TUDSSL/condenar/Hardware/PCBs/CPUModule/panel/readme.md

 kikit panelize     --layout 'grid; rows: 1; cols: 1; space: 2mm'     --tabs 'fixed; width: 3mm; vcount: 2'     --cuts 'mousebites; drill: 0.5mm; spacing: 1mm; offset: -0.15mm; prolong: 0.5mm'     --framing 'frame; width: 5mm; space: 3mm; cuts: h'     --post 'millradius: 1mm'     ../cpu-module.kicad_pcb cpu-module-panel.kicad_pcb
