TUDSSL/condenar/Data/ConsoleBenchmarks/SSD1963_PowerConsumption.xlsx

 |  |  |  | Power consumption [mA]
 |  |  |  |  |  | CLK settings
 |  |  |  |  |  | APO 48MHz | APO 24MHz | APO 12MHz | APO 6MHz | XTAL -> 6MHz | XTAL -> PLL 100MHz | XTAL -> PLL 50MHz | APO -> PLL 100MHz | APO -> PLL 50MHz
40Hz | 4.4 | APO_48MHz, 10Hz | 1.8mA | FPS | 10Hz | 1.8 | 1.05 | 0.67 | 0.47 | 0.725 | 4.2 | 2.7 | 3.95 | 2.45
20Hz | 2.7 | APO_48MHz, 20Hz | 1.92mA |  | 20Hz | 1.92 | 1.08 | 0.77 | 0.58 | 0.839 | 4.3 | 2.8 | 4.09 | 2.53
10Hz | 1.86 | APO_48MHz, 40Hz | 2.14mA |  | 40Hz | 2.14 | 1.37 | 0.98 |  |  | 4.4 | 3 | 4.3 | 2.75
 |  | APO_24MHz, 10Hz | 1.05mA
 |  | APO_24MHz, 20Hz | 1.08mA
 |  | APO_24MHz, 40Hz | 1.37mA
