TUDSSL/condenar/Data/MainStudy/Data/SurveyResults/Complete_Survey_Data.csv

participant_id | experiment_option | lux_level | freq_gaming_background | fps_background | puzzle_background | doom_background | tetris_background | power_harvesting_background | device_type | performance_effort | temporal_frustration | effort_temporal | physical_frustration | performance_frustration | physical_temporal | performance_physical | mental_temporal | effort_frustration | mental_performance | performance_temporal | mental_effort | mental_physical | effort_physical | mental_frustration | tetris_a_experience_vs_doing | tetris_a_emotional_attachment | tetris_a_interest_in_progress | tetris_a_desire_to_speak | tetris_a_disappointment_when_interrupted | tetris_a_desire_to_play_again | tetris_a_mental_demand | tetris_a_physical_demand | tetris_a_hurried_pace | tetris_a_success_accomplishment | tetris_a_effort | tetris_a_insecurity_irritation | doom_a_experience_vs_doing | doom_a_emotional_attachment | doom_a_interest_in_progress | doom_a_desire_to_speak | doom_a_disappointment_when_interrupted | doom_a_desire_to_play_again | doom_a_mental_demand | doom_a_physical_demand | doom_a_hurried_pace | doom_a_success_accomplishment | doom_a_effort | doom_a_insecurity_irritation |
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
