TUDSSL/condenar/Software/Console/games/Gameboy/GBA/emulator/gba/MMU.cpp

#include "../common/Port.h"
#include "../common/Settings.h"
#include "Cartridge.h"
#include "CPU.h"
#include "GBA.h"
#include "Globals.h"
#include <cstdio>
#include "string.h"
#include "Helpers/Flash.h"


extern "C"{
	uint32_t am_util_stdio_printf(const char *pcFmt, ...);
}



extern bool stopState;
extern bool timer0On;
extern int timer0Ticks;
extern int timer0ClockReload;
extern bool timer1On;
extern int timer1Ticks;
extern int timer1ClockReload;
extern bool timer2On;
extern int timer2Ticks;
extern int timer2ClockReload;
extern bool timer3On;
extern int timer3Ticks;
extern int timer3ClockReload;

namespace MMU
{

static bool ioReadable[0x400];

template <typename T>
static inline T readLE(u8* x)
{
	return *((T *)x);
}

template <typename T>
static inline void writeLE(u8* x, T value)
{
	*((T *)x) = value;
}

// Memory read functions forward declarations
template<typename T>
static T unreadable(u32 address);

template<int s, typename T>
static T readGeneric(u32 address);

template<typename T, int mask>
static T readBios(u32 address);
 
template<typename T>
static T readVRAM(u32 address);

static u8 readIo8(u32 address);
static u16 readIo16(u32 address);
static u32 readIo32(u32 address);

// Memory write functions forward declarations
template<typename T>
static void unwritable(u32 address, T value);
 
template<int s, typename T>
static void writeGeneric(u32 address, T value);

template<int s>
static void writeVideo8(u32 address, u8 value);

template<typename T>
static void writeVRAM(u32 address, T value);

template<>
void writeVRAM<u8>(u32 address, u8 value);

static void writeIo8(u32 address, u8 value);
static void writeIo16(u32 address, u16 value);
static void writeIo32(u32 address, u32 value);

// Memory map definition
struct MemAccess
{
	u8 *mem;
	const u32 mask;
	u8 (*read8)(u32);
	u16 (*read16)(u32);
	u32 (*read32)(u32);
	void (*write8)(u32, u8);
	void (*write16)(u32, u16);
	void (*write32)(u32, u32);
};

static MemAccess memMap[] =
{
	{ 0, 0x00003FFF, readBios<u8, 0x03>, readBios<u16, 0x02>, readBios<u32, 0x0F>, unwritable<u8>,      unwritable<u16>,      unwritable<u32>      }, // 0 - bios - mask values are probably wrong
	{ 0, 0x00000000, unreadable<u8>,     unreadable<u16>,     unreadable<u32>,     unwritable<u8>,      unwritable<u16>,      unwritable<u32>      }, // 1
	{ 0, 0x0003FFFF, readGeneric<2, u8>, readGeneric<2, u16>, readGeneric<2, u32>, writeGeneric<2, u8>, writeGeneric<2, u16>, writeGeneric<2, u32> }, // 2
	{ 0, 0x00007FFF, readGeneric<3, u8>, readGeneric<3, u16>, readGeneric<3, u32>, writeGeneric<3, u8>, writeGeneric<3, u16>, writeGeneric<3, u32> }, // 3
	{ 0, 0x000003FF, readIo8,            readIo16,            readIo32,            writeIo8,            writeIo16,            writeIo32            }, // 4
	{ 0, 0x000003FF, readGeneric<5, u8>, readGeneric<5, u16>, readGeneric<5, u32>, writeVideo8<5>,      writeGeneric<5, u16>, writeGeneric<5, u32> }, // 5
	{ 0, 0x0001FFFF, readVRAM<u8>,       readVRAM<u16>,       readVRAM<u32>,       writeVRAM<u8>,       writeVRAM<u16>,       writeVRAM<u32>       }, // 6
	{ 0, 0x000003FF, readGeneric<7, u8>, readGeneric<7, u16>, readGeneric<7, u32>, unwritable<u8>,      writeGeneric<7, u16>, writeGeneric<7, u32> }, // 7
	{ 0, 0xFFFFFFFF, cartridge_read8,   cartridge_read16,   cartridge_read32,   cartridge_write8,   cartridge_write16,   cartridge_write32   }, // 8
	{ 0, 0xFFFFFFFF, cartridge_read8,   cartridge_read16,   cartridge_read32,   cartridge_write8,   cartridge_write16,   cartridge_write32   }, // 9
	{ 0, 0xFFFFFFFF, cartridge_read8,   cartridge_read16,   cartridge_read32,   cartridge_write8,   cartridge_write16,   cartridge_write32   }, // 10
	{ 0, 0xFFFFFFFF, cartridge_read8,   cartridge_read16,   cartridge_read32,   cartridge_write8,   cartridge_write16,   cartridge_write32   }, // 11
	{ 0, 0xFFFFFFFF, cartridge_read8,   cartridge_read16,   cartridge_read32,   cartridge_write8,   cartridge_write16,   cartridge_write32   }, // 12
	{ 0, 0xFFFFFFFF, cartridge_read8,   cartridge_read16,   cartridge_read32,   cartridge_write8,   cartridge_write16,   cartridge_write32   }, // 13
	{ 0, 0xFFFFFFFF, cartridge_read8,   cartridge_read16,   cartridge_read32,   cartridge_write8,   cartridge_write16,   cartridge_write32   }  // 14
};

// MMU public functions
bool init()
{	
	//Fast clear of the memory, just in case
	memset((uint8_t*)SRAM_XIP_BASE_ADDRESS, 0, 0x40000 + 0x4000 + 0x8000 + 0x400 + 0x20000 + 0x400 + 0x400);


	workRAM     = (uint8_t*)SRAM_XIP_BASE_ADDRESS; //   new u8[0x40000];
	bios        = workRAM + 0x40000; //new u8[0x4000];
	internalRAM = bios + 0x4000; //new u8[0x8000];
	paletteRAM  = internalRAM + 0x8000; //new u8[0x400];
	vram        = paletteRAM + 0x400; //new u8[0x20000];
	oam         = vram + 0x20000; //new u8[0x400];
	ioMem       = oam + 0x400; //new u8[0x400];
	//End of shared memory used: (ioMem + 0x400). Total memory: 445,440B







	memMap[0].mem = bios;
	memMap[2].mem = workRAM;
	memMap[3].mem = internalRAM;
	memMap[4].mem = ioMem;
	memMap[5].mem = paletteRAM;
	memMap[6].mem = vram;
	memMap[7].mem = oam;
	
	for (int i = 0; i < 0x400; i++)
		ioReadable[i] = true;
	for (int i = 0x10; i < 0x48; i++)
		ioReadable[i] = false;
	for (int i = 0x4c; i < 0x50; i++)
		ioReadable[i] = false;
	for (int i = 0x54; i < 0x60; i++)
		ioReadable[i] = false;
	for (int i = 0x8c; i < 0x90; i++)
		ioReadable[i] = false;
	for (int i = 0xa0; i < 0xb8; i++)
		ioReadable[i] = false;
	for (int i = 0xbc; i < 0xc4; i++)
		ioReadable[i] = false;
	for (int i = 0xc8; i < 0xd0; i++)
		ioReadable[i] = false;
	for (int i = 0xd4; i < 0xdc; i++)
		ioReadable[i] = false;
	for (int i = 0xe0; i < 0x100; i++)
		ioReadable[i] = false;
	for (int i = 0x110; i < 0x120; i++)
		ioReadable[i] = false;
	for (int i = 0x12c; i < 0x130; i++)
		ioReadable[i] = false;
	for (int i = 0x138; i < 0x140; i++)
		ioReadable[i] = false;
	for (int i = 0x144; i < 0x150; i++)
		ioReadable[i] = false;
	for (int i = 0x15c; i < 0x200; i++)
		ioReadable[i] = false;
	for (int i = 0x20c; i < 0x300; i++)
		ioReadable[i] = false;
	for (int i = 0x304; i < 0x400; i++)
		ioReadable[i] = false;

	return true;
}


u32 read32(u32 address)
{
 #ifdef GBA_LOGGING
	if (address & 3)
	{
		if (settings_log_channel_enabled(LOG_UNALIGNED_MEMORY))
 		{
			am_util_stdio_printf("Unaligned word read: %08x at %08x\n", address, CPU::armMode ?
 			    CPU::armNextPC - 4 : CPU::armNextPC - 2);
 		}
	}
 #endif
 
	// Reads must be 32 bits aligned
	u32 value =  memMap[address >> 24].read32(address & 0xFFFFFFFC);
 
 	if (address & 3)
 	{
 		int shift = (address & 3) << 3;
 		value = (value >> shift) | (value << (32 - shift));
 	}

 	return value;
 }
 
u32 read16(u32 address)
 {
 #ifdef GBA_LOGGING
 	if (address & 1)
	{
		if (settings_log_channel_enabled(LOG_UNALIGNED_MEMORY))
		{
			am_util_stdio_printf("Unaligned word read: %08x at %08x\n", address, CPU::armMode ?
			    CPU::armNextPC - 4 : CPU::armNextPC - 2);
		}
	}
#endif

	// Reads must be 16 bits aligned
	u16 value = memMap[address >> 24].read16(address & 0xFFFFFFFE);

	if (address & 1)
	{
		value = (value >> 8) | (value << 24);
	}

	return value;
}

u16 read16s(u32 address)
{
	u16 value = read16(address);
	if ((address & 1))
		value = (s8)value;
	return value;
}

u8 read8(u32 address)
{
	return memMap[address >> 24].read8(address);
}

void write32(u32 address, u32 value)
{
#ifdef GBA_LOGGING
	if (address & 3)
	{
		if (settings_log_channel_enabled(LOG_UNALIGNED_MEMORY))
		{
			am_util_stdio_printf("Unaligned word write: %08x to %08x from %08x\n",
			    value,
			    address,
			    CPU::armMode ? CPU::armNextPC - 4 : CPU::armNextPC - 2);
		}
	}
#endif

	memMap[address >> 24].write32(address & 0xFFFFFFFC, value);
}

void write16(u32 address, u16 value)
{
#ifdef GBA_LOGGING
	if (address & 1)
	{
		if (settings_log_channel_enabled(LOG_UNALIGNED_MEMORY))
		{
			am_util_stdio_printf("Unaligned halfword write: %04x to %08x from %08x\n",
			    value,
			    address,
			    CPU::armMode ? CPU::armNextPC - 4 : CPU::armNextPC - 2);
		}
	}
#endif

	memMap[address >> 24].write16(address & 0xFFFFFFFE, value);
}

void write8(u32 address, u8 b)
{
	memMap[address >> 24].write8(address, b);
}

// Memory read functions implementations
template<typename T>
static T unreadable(u32 address)
{
#ifdef GBA_LOGGING
		if (settings_log_channel_enabled(LOG_ILLEGAL_READ))
		{
			am_util_stdio_printf("Illegal read: %08x at %08x\n", address, CPU::armMode ?
			    CPU::armNextPC - 4 : CPU::armNextPC - 2);
		}
#endif

	return 0;
}

template<int s, typename T>
static T readGeneric(u32 address)
{
	u32 mask = memMap[s].mask;

	return readLE<T>(&memMap[s].mem[address & mask]);
}

template<typename T, int mask>
static T readBios(u32 address)
{
	T value;

	if (CPU::reg[15].I >> 24)
	{
		// TODO: proper handling of reading unreadable bios memory, without "biosProtected"
		if (address < 0x4000)
		{
			value = readLE<T>(&biosProtected[address & mask]);
			//LOG_I("Reading protected bios memory %d %d\n", address, value);
		}
		else
		{
			value = unreadable<T>(address);
		}
	}
	else
		value = readGeneric<0, T>(address);

	return value;
}

static u8 readIo8(u32 address)
{
	if ((address < 0x4000400) && ioReadable[address & 0x3FF])
	{
		return readGeneric<4, u8>(address);
	}
	else
	{
		return unreadable<u8>(address);
	}
}

static u16 readIo16(u32 address)
{
	u16 value;

	if ((address < 0x4000400) && ioReadable[address & 0x3FF])
	{
		value = readGeneric<4, u16>(address);
		if (((address & 0x3fe)>0xFF) && ((address & 0x3fe)<0x10E))
		{
			if (((address & 0x3fe) == 0x100) && timer0On)
				value = 0xFFFF - ((timer0Ticks-cpuTotalTicks) >> timer0ClockReload);
			else
				if (((address & 0x3fe) == 0x104) && timer1On && !(TM1CNT & 4))
					value = 0xFFFF - ((timer1Ticks-cpuTotalTicks) >> timer1ClockReload);
				else
					if (((address & 0x3fe) == 0x108) && timer2On && !(TM2CNT & 4))
						value = 0xFFFF - ((timer2Ticks-cpuTotalTicks) >> timer2ClockReload);
					else
						if (((address & 0x3fe) == 0x10C) && timer3On && !(TM3CNT & 4))
							value = 0xFFFF - ((timer3Ticks-cpuTotalTicks) >> timer3ClockReload);
		}
	}
	else
	{
		value = unreadable<u16>(address);
	}

	return value;
}

static u32 readIo32(u32 address)
{
	u32 value;

	if ((address < 0x4000400) && ioReadable[address & 0x3FF])
	{
		if (ioReadable[(address & 0x3FF) + 2])
			value = readGeneric<4, u32>(address);
		else
			value = readGeneric<4, u16>(address);
	}
	else
	{
		value = unreadable<u32>(address);
	}

	return value;
}

template<typename T>
static T readVRAM(u32 address)
{
	address &= 0x1FFFF;

	if (((DISPCNT & 7) > 2) && ((address & 0x1C000) == 0x18000))
	{
		return 0;
	}
	if ((address & 0x18000) == 0x18000)
	{
		address &= 0x17FFF;
	}

	return readGeneric<6, T>(address);
}

// Memory write functions implementations
template<typename T>
static void unwritable(u32 address, T value)
{
#ifdef GBA_LOGGING
	if (settings_log_channel_enabled(LOG_ILLEGAL_WRITE))
	{
		am_util_stdio_printf("Illegal write: %02x to %08x from %08x\n",
			value,
			address,
			CPU::armMode ? CPU::armNextPC - 4 : CPU::armNextPC - 2);
	}
#endif
}

template<int s, typename T>
static void writeGeneric(u32 address, T value)
{
	u32 mask = memMap[s].mask;

	writeLE<T>(&memMap[s].mem[address & mask], value);
}

template<int s>
static void writeVideo8(u32 address, u8 value)
{
	writeGeneric<s, u16>(address & 0xFFFFFFFE, (value << 8) | value);
}

template<typename T>
static void writeVRAM(u32 address, T value)
{
	address = (address & 0x1FFFF);
	if (((DISPCNT & 7) > 2) && ((address & 0x1C000) == 0x18000))
		return;
	if ((address & 0x18000) == 0x18000)
		address &= 0x17FFF;

	writeGeneric<6, T>(address, value);
}

template<>
void writeVRAM<u8>(u32 address, u8 value)
{
	static const u32 objTilesAddress [3] = {0x010000, 0x014000, 0x014000};

	address &= 0x1FFFF;
	if (((DISPCNT & 7) > 2) && ((address & 0x1C000) == 0x18000))
		return;
	if ((address & 0x18000) == 0x18000)
		address &= 0x17FFF;

	// byte writes to OBJ VRAM are ignored
	if (address < objTilesAddress[((DISPCNT&7)+1)>>2])
	{
		writeVideo8<6>(address, value);
	}
}

static void writeIo8(u32 address, u8 value)
{
	if (address < 0x4000400)
	{
		switch (address & 0x3FF)
		{
		case 0x60:
		case 0x61:
		case 0x62:
		case 0x63:
		case 0x64:
		case 0x65:
		case 0x68:
		case 0x69:
		case 0x6c:
		case 0x6d:
		case 0x70:
		case 0x71:
		case 0x72:
		case 0x73:
		case 0x74:
		case 0x75:
		case 0x78:
		case 0x79:
		case 0x7c:
		case 0x7d:
		case 0x80:
		case 0x81:
		case 0x84:
		case 0x85:
		case 0x90:
		case 0x91:
		case 0x92:
		case 0x93:
		case 0x94:
		case 0x95:
		case 0x96:
		case 0x97:
		case 0x98:
		case 0x99:
		case 0x9a:
		case 0x9b:
		case 0x9c:
		case 0x9d:
		case 0x9e:
		case 0x9f:
			//soundEvent(address & 0xFF, value);
			break;
		case 0x301: // HALTCNT, undocumented
			if (value == 0x80)
				stopState = true;
			holdState = 1;
			cpuNextEvent = cpuTotalTicks;
			break;
		default: // every other register
			u32 lowerBits = address & 0x3fe;
			if (address & 1)
			{
				CPUUpdateRegister(lowerBits, (READ16LE(&ioMem[lowerBits]) & 0x00FF) | (value << 8));
			}
			else
			{
				CPUUpdateRegister(lowerBits, (READ16LE(&ioMem[lowerBits]) & 0xFF00) | value);
			}
		}
	}
	else
	{
		unwritable<u8>(address, value);
	}
}

static void writeIo16(u32 address, u16 value)
{
	if (address < 0x4000400)
	{
		CPUUpdateRegister(address & 0x3FF, value);
	}
	else
	{
		unwritable<u16>(address, value);
	}
}

static void writeIo32(u32 address, u32 value)
{
	if (address < 0x4000400)
	{
		CPUUpdateRegister((address & 0x3FF), value & 0xFFFF);
		CPUUpdateRegister((address & 0x3FF) + 2, (value >> 16));
	}
	else
	{
		unwritable<u32>(address, value);
	}
}

} // namespace MMU
