TUDSSL/condenar/Software/Console/games/Gameboy/GBA/emulator/gba/Globals.c

// VisualBoyAdvance - Nintendo Gameboy/GameboyAdvance (TM) emulator.
// Copyright (C) 1999-2003 Forgotten
// Copyright (C) 2005-2006 Forgotten and the VBA development team

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
#include "Globals.h"

int layerEnable = 0xff00;

u8 *bios = 0;
u8 *internalRAM = 0;
u8 *workRAM = 0;
u8 *paletteRAM = 0;
u8 *vram = 0;
u8 *oam = 0;
u8 *ioMem = 0;

/*
	workRAM     = new u8[0x40000];
	bios        = new u8[0x4000];
	internalRAM = new u8[0x8000];
	paletteRAM  = new u8[0x400];
	vram        = new u8[0x20000];
	oam         = new u8[0x400];
	ioMem       = new u8[0x400];
*/

u16 DISPCNT  = 0x0080;
u16 DISPSTAT = 0x0000;
u16 VCOUNT   = 0x0000;
u16 BG0CNT   = 0x0000;
u16 BG1CNT   = 0x0000;
u16 BG2CNT   = 0x0000;
u16 BG3CNT   = 0x0000;
u16 BG0HOFS  = 0x0000;
u16 BG0VOFS  = 0x0000;
u16 BG1HOFS  = 0x0000;
u16 BG1VOFS  = 0x0000;
u16 BG2HOFS  = 0x0000;
u16 BG2VOFS  = 0x0000;
u16 BG3HOFS  = 0x0000;
u16 BG3VOFS  = 0x0000;
u16 BG2PA    = 0x0100;
u16 BG2PB    = 0x0000;
u16 BG2PC    = 0x0000;
u16 BG2PD    = 0x0100;
u16 BG2X_L   = 0x0000;
u16 BG2X_H   = 0x0000;
u16 BG2Y_L   = 0x0000;
u16 BG2Y_H   = 0x0000;
u16 BG3PA    = 0x0100;
u16 BG3PB    = 0x0000;
u16 BG3PC    = 0x0000;
u16 BG3PD    = 0x0100;
u16 BG3X_L   = 0x0000;
u16 BG3X_H   = 0x0000;
u16 BG3Y_L   = 0x0000;
u16 BG3Y_H   = 0x0000;
u16 WIN0H    = 0x0000;
u16 WIN1H    = 0x0000;
u16 WIN0V    = 0x0000;
u16 WIN1V    = 0x0000;
u16 WININ    = 0x0000;
u16 WINOUT   = 0x0000;
u16 MOSAIC   = 0x0000;
u16 BLDMOD   = 0x0000;
u16 COLEV    = 0x0000;
u16 COLY     = 0x0000;
u16 DM0SAD_L = 0x0000;
u16 DM0SAD_H = 0x0000;
u16 DM0DAD_L = 0x0000;
u16 DM0DAD_H = 0x0000;
u16 DM0CNT_L = 0x0000;
u16 DM0CNT_H = 0x0000;
u16 DM1SAD_L = 0x0000;
u16 DM1SAD_H = 0x0000;
u16 DM1DAD_L = 0x0000;
u16 DM1DAD_H = 0x0000;
u16 DM1CNT_L = 0x0000;
u16 DM1CNT_H = 0x0000;
u16 DM2SAD_L = 0x0000;
u16 DM2SAD_H = 0x0000;
u16 DM2DAD_L = 0x0000;
u16 DM2DAD_H = 0x0000;
u16 DM2CNT_L = 0x0000;
u16 DM2CNT_H = 0x0000;
u16 DM3SAD_L = 0x0000;
u16 DM3SAD_H = 0x0000;
u16 DM3DAD_L = 0x0000;
u16 DM3DAD_H = 0x0000;
u16 DM3CNT_L = 0x0000;
u16 DM3CNT_H = 0x0000;
u16 TM0D     = 0x0000;
u16 TM0CNT   = 0x0000;
u16 TM1D     = 0x0000;
u16 TM1CNT   = 0x0000;
u16 TM2D     = 0x0000;
u16 TM2CNT   = 0x0000;
u16 TM3D     = 0x0000;
u16 TM3CNT   = 0x0000;
u16 P1       = 0xFFFF;
u16 IE       = 0x0000;
u16 IF       = 0x0000;
u16 IME      = 0x0000;
