TUDSSL/condenar/Software/Console/games/Gameboy/GBA/emulator/gba/Globals.h

// VisualBoyAdvance - Nintendo Gameboy/GameboyAdvance (TM) emulator.
// Copyright (C) 1999-2003 Forgotten
// Copyright (C) 2005-2006 Forgotten and the VBA development team

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
#ifndef VBAM_GBA_GLOBALS_H_
#define VBAM_GBA_GLOBALS_H_

#include <glib.h>
#include "../common/Types.h"

/* Set up for C function definitions, even when using C++ */
#ifdef __cplusplus
extern "C" {
#endif

extern int layerEnable;

extern u8 *bios;
extern u8 *internalRAM;
extern u8 *workRAM;
extern u8 *paletteRAM;
extern u8 *vram;
extern u8 *oam;
extern u8 *ioMem;

extern u16 DISPCNT;
extern u16 DISPSTAT;
extern u16 VCOUNT;
extern u16 BG0CNT;
extern u16 BG1CNT;
extern u16 BG2CNT;
extern u16 BG3CNT;
extern u16 BG0HOFS;
extern u16 BG0VOFS;
extern u16 BG1HOFS;
extern u16 BG1VOFS;
extern u16 BG2HOFS;
extern u16 BG2VOFS;
extern u16 BG3HOFS;
extern u16 BG3VOFS;
extern u16 BG2PA;
extern u16 BG2PB;
extern u16 BG2PC;
extern u16 BG2PD;
extern u16 BG2X_L;
extern u16 BG2X_H;
extern u16 BG2Y_L;
extern u16 BG2Y_H;
extern u16 BG3PA;
extern u16 BG3PB;
extern u16 BG3PC;
extern u16 BG3PD;
extern u16 BG3X_L;
extern u16 BG3X_H;
extern u16 BG3Y_L;
extern u16 BG3Y_H;
extern u16 WIN0H;
extern u16 WIN1H;
extern u16 WIN0V;
extern u16 WIN1V;
extern u16 WININ;
extern u16 WINOUT;
extern u16 MOSAIC;
extern u16 BLDMOD;
extern u16 COLEV;
extern u16 COLY;
extern u16 DM0SAD_L;
extern u16 DM0SAD_H;
extern u16 DM0DAD_L;
extern u16 DM0DAD_H;
extern u16 DM0CNT_L;
extern u16 DM0CNT_H;
extern u16 DM1SAD_L;
extern u16 DM1SAD_H;
extern u16 DM1DAD_L;
extern u16 DM1DAD_H;
extern u16 DM1CNT_L;
extern u16 DM1CNT_H;
extern u16 DM2SAD_L;
extern u16 DM2SAD_H;
extern u16 DM2DAD_L;
extern u16 DM2DAD_H;
extern u16 DM2CNT_L;
extern u16 DM2CNT_H;
extern u16 DM3SAD_L;
extern u16 DM3SAD_H;
extern u16 DM3DAD_L;
extern u16 DM3DAD_H;
extern u16 DM3CNT_L;
extern u16 DM3CNT_H;
extern u16 TM0D;
extern u16 TM0CNT;
extern u16 TM1D;
extern u16 TM1CNT;
extern u16 TM2D;
extern u16 TM2CNT;
extern u16 TM3D;
extern u16 TM3CNT;
extern u16 P1;
extern u16 IE;
extern u16 IF;
extern u16 IME;

#ifdef __GNUC__
//# define INSN_REGPARM __attribute__((regparm(1))) //Not supported in ARM??
# define INSN_REGPARM /*nothing*/
# define LIKELY(x) __builtin_expect(!!(x),1)
# define UNLIKELY(x) __builtin_expect(!!(x),0)
#else
# define INSN_REGPARM /*nothing*/
# define LIKELY(x) (x)
# define UNLIKELY(x) (x)
#endif

/* Ends C function definitions when using C++ */
#ifdef __cplusplus
}
#endif

#endif // VBAM_GBA_GLOBALS_H_
